ccadic/ZE32U4-KB/kailh-keys3.jpg

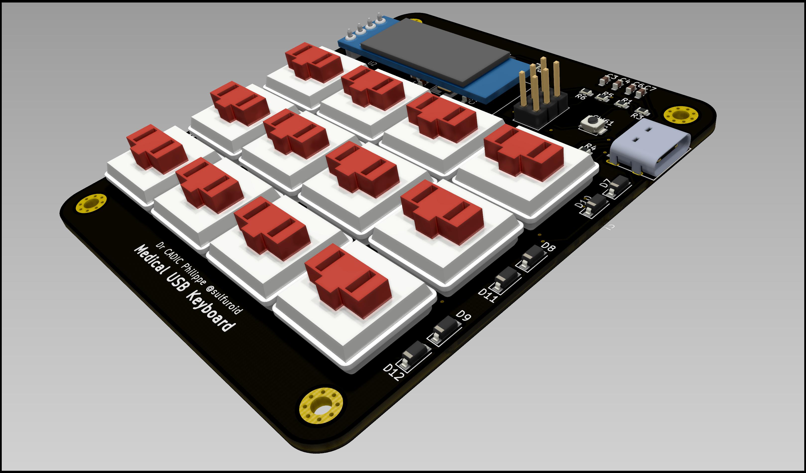
kailh-keys3.jpg
